waitingate/ESP32-S3_Vehicle_Warning_System/images/app_demo/screenshots/02_remotexy_home_20260102-160005.png

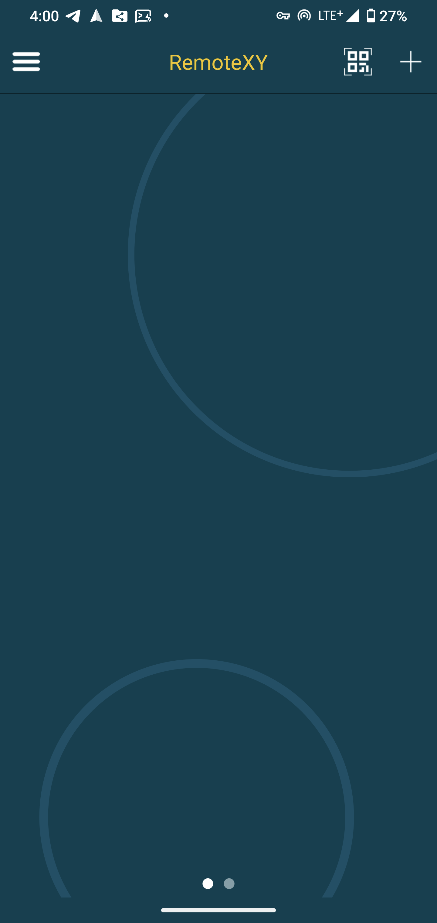
images/app_demo/screenshots/02_remotexy_home_20260102-160005.png
