waitingate/ESP32-S3_Vehicle_Warning_System/images/app_demo/screenshots/03_add_new_device_20260102-160010.png

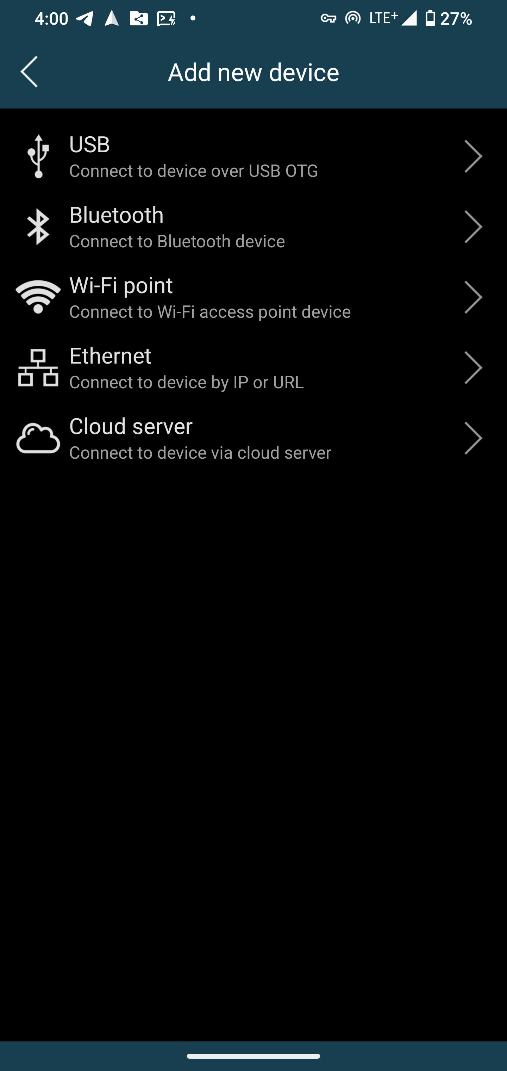
images/app_demo/screenshots/03_add_new_device_20260102-160010.png
