waitingate/ESP32-S3_Vehicle_Warning_System/images/app_demo/screenshots/04_choose_ble_20260102-160016.png

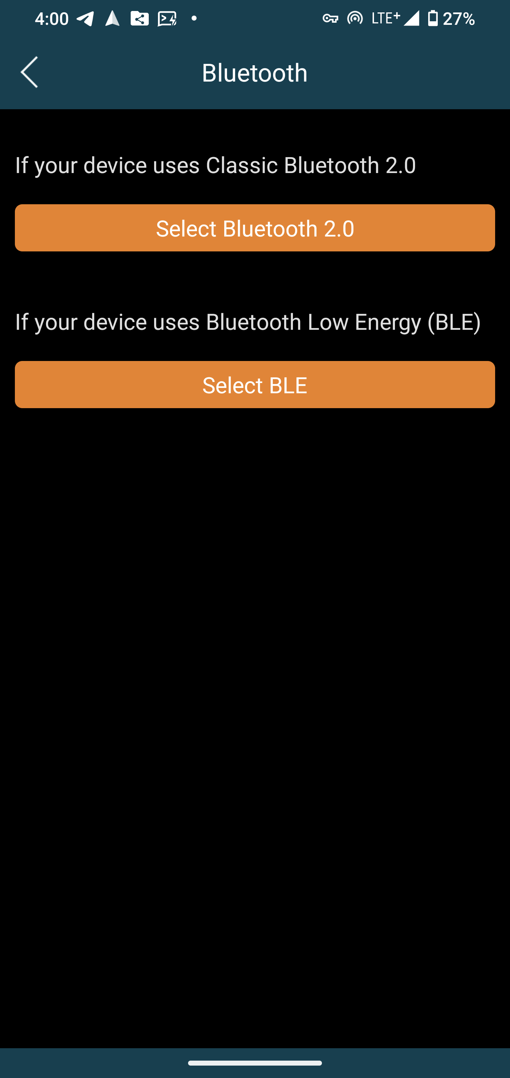
images/app_demo/screenshots/04_choose_ble_20260102-160016.png
