waitingate/ESP32-S3_Vehicle_Warning_System/images/app_demo/screenshots/05_choose_device_smart_warning_20260102-160021.png

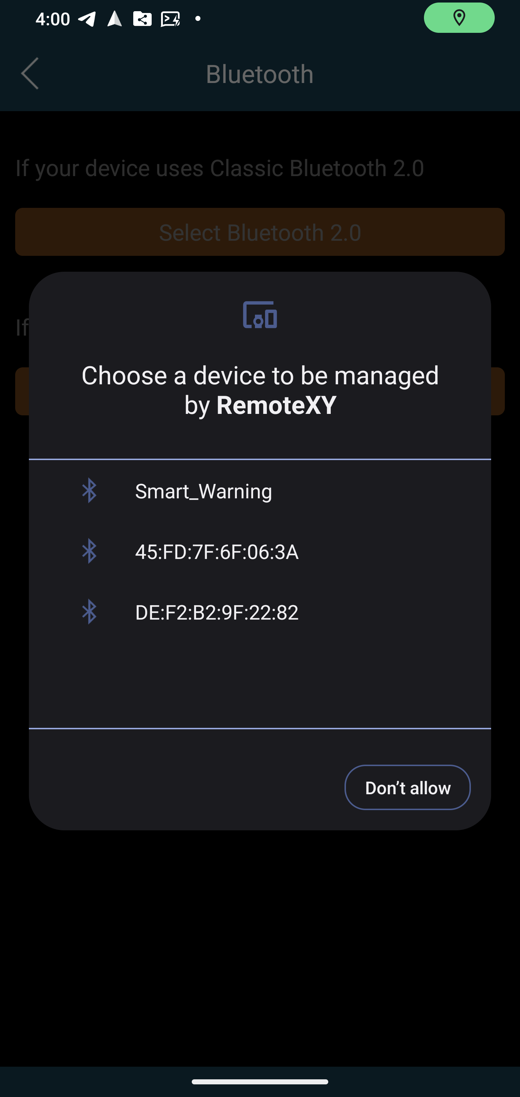
images/app_demo/screenshots/05_choose_device_smart_warning_20260102-160021.png
