waitingate/ESP32-S3_Vehicle_Warning_System/images/app_demo/screenshots/06_connecting_log_20260102-160028.png

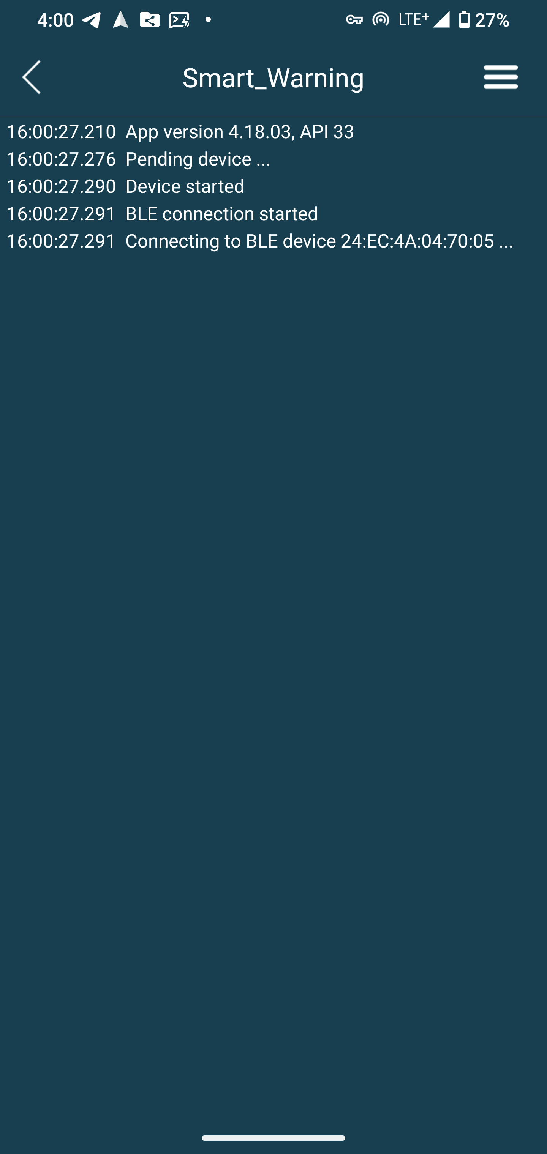
images/app_demo/screenshots/06_connecting_log_20260102-160028.png
