waitingate/ESP32-S3_Vehicle_Warning_System/images/app_demo/screenshots/11_menu_triangle_light_20260102-160242.png

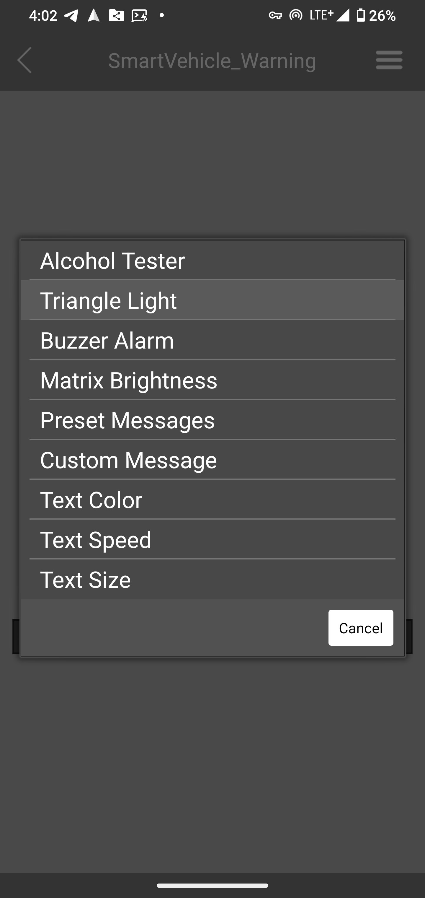
images/app_demo/screenshots/11_menu_triangle_light_20260102-160242.png
