waitingate/ESP32-S3_Vehicle_Warning_System/images/app_demo/screenshots/12_triangle_light_on_20260102-160249.png

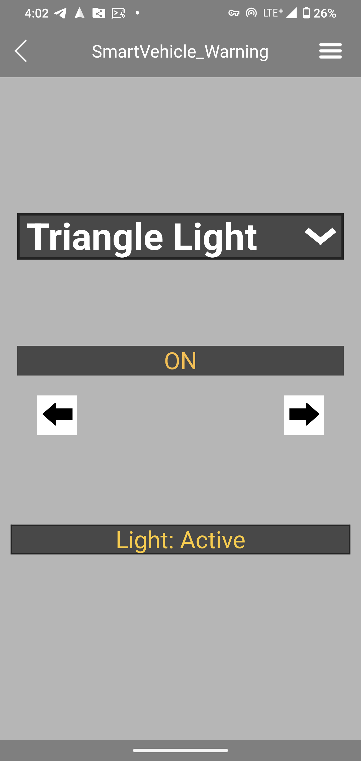
images/app_demo/screenshots/12_triangle_light_on_20260102-160249.png
