waitingate/ESP32-S3_Vehicle_Warning_System/images/app_demo/screenshots/13_triangle_light_off_20260102-160254.png

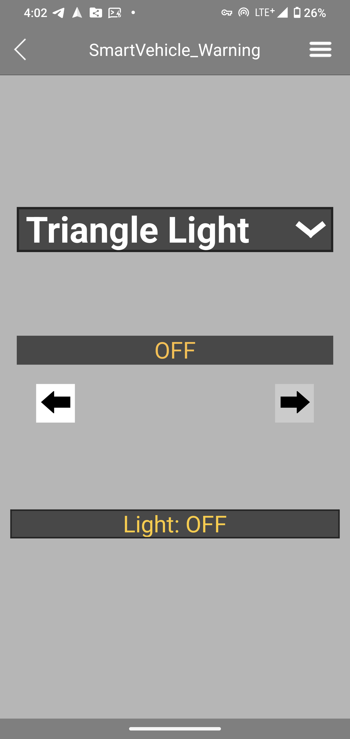
images/app_demo/screenshots/13_triangle_light_off_20260102-160254.png
