waitingate/ESP32-S3_Vehicle_Warning_System/images/app_demo/screenshots/16_buzzer_volume_0_20260102-160329.png

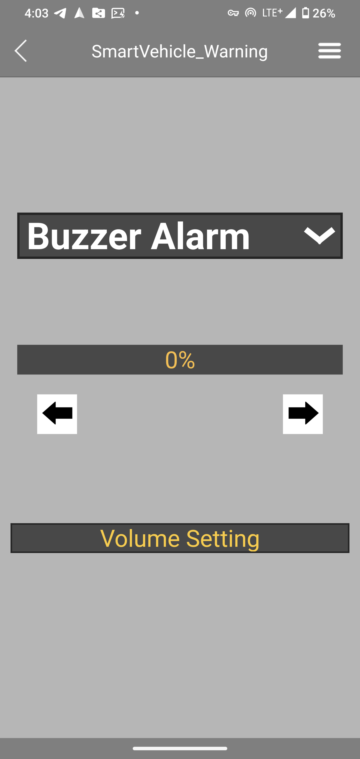
images/app_demo/screenshots/16_buzzer_volume_0_20260102-160329.png
