waitingate/ESP32-S3_Vehicle_Warning_System/images/app_demo/screenshots/22_preset_message_mode_1_20260102-160438.png

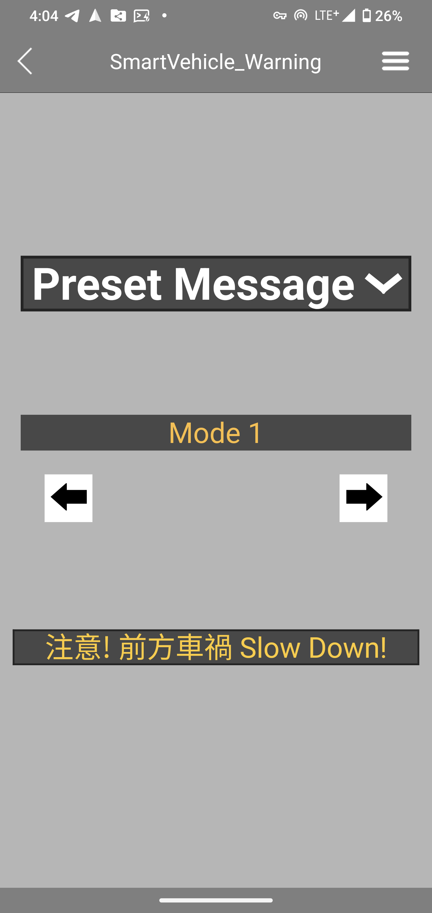
images/app_demo/screenshots/22_preset_message_mode_1_20260102-160438.png
