waitingate/ESP32-S3_Vehicle_Warning_System/images/app_demo/screenshots/26_custom_message_typing_20260102-160552.png

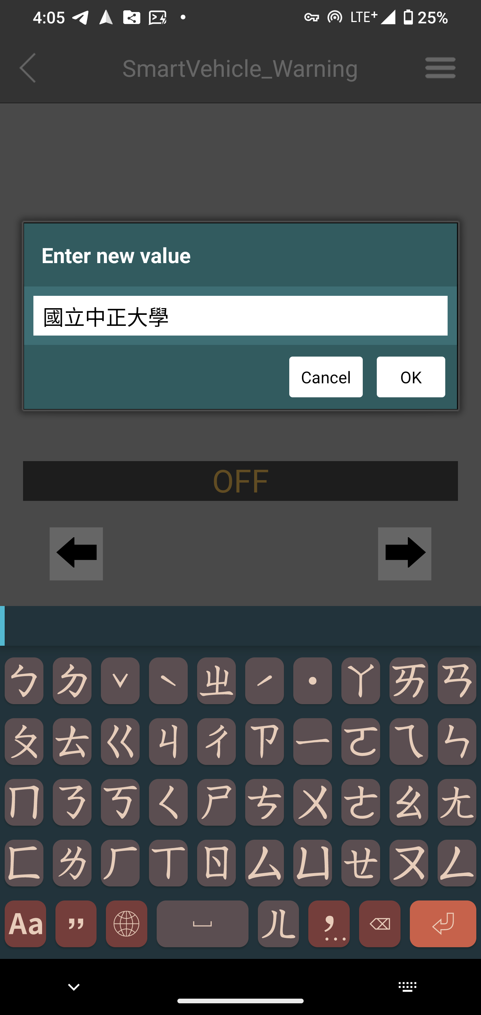
images/app_demo/screenshots/26_custom_message_typing_20260102-160552.png
