waitingate/ESP32-S3_Vehicle_Warning_System/images/app_demo/screenshots/27_custom_message_new_text_off_20260102-160559.png

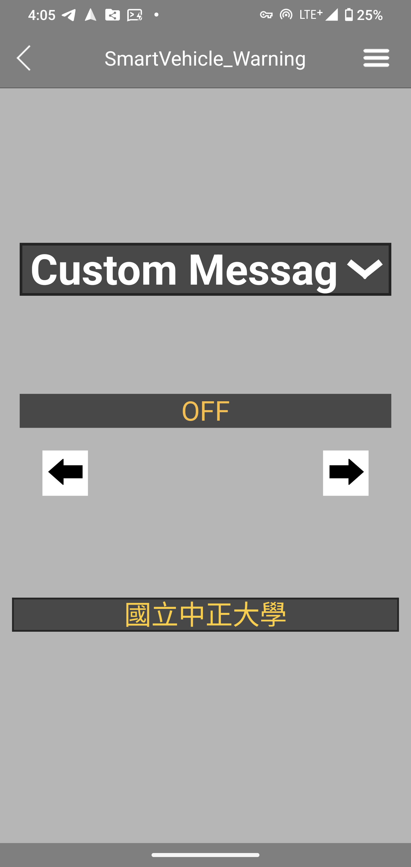
images/app_demo/screenshots/27_custom_message_new_text_off_20260102-160559.png
