waitingate/ESP32-S3_Vehicle_Warning_System/images/app_demo/screenshots/30_text_color_rainbow_20260102-160642.png

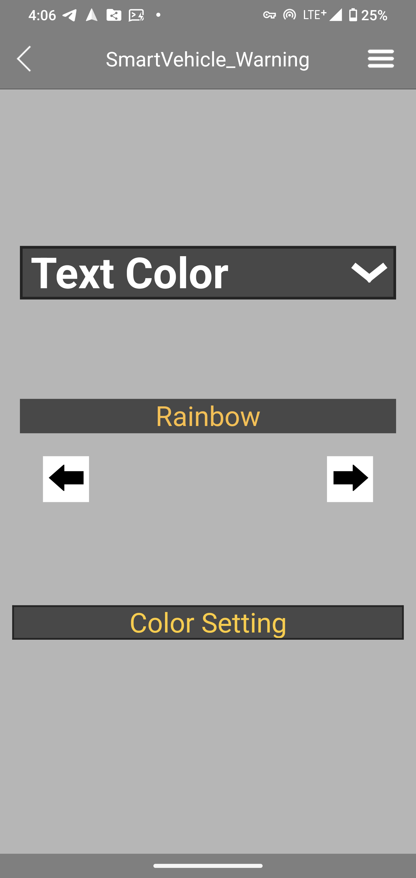
images/app_demo/screenshots/30_text_color_rainbow_20260102-160642.png
