waitingate/ESP32-S3_Vehicle_Warning_System/images/app_demo/screenshots/09_alcohol_tester_ppm_20260102-160043.png

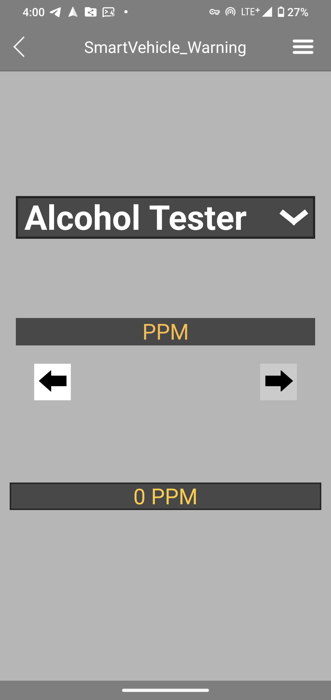
images/app_demo/screenshots/09_alcohol_tester_ppm_20260102-160043.png
